Ernestoflores27/Garden_Defender/Mechanical Design/Renders/V2/1.JPG

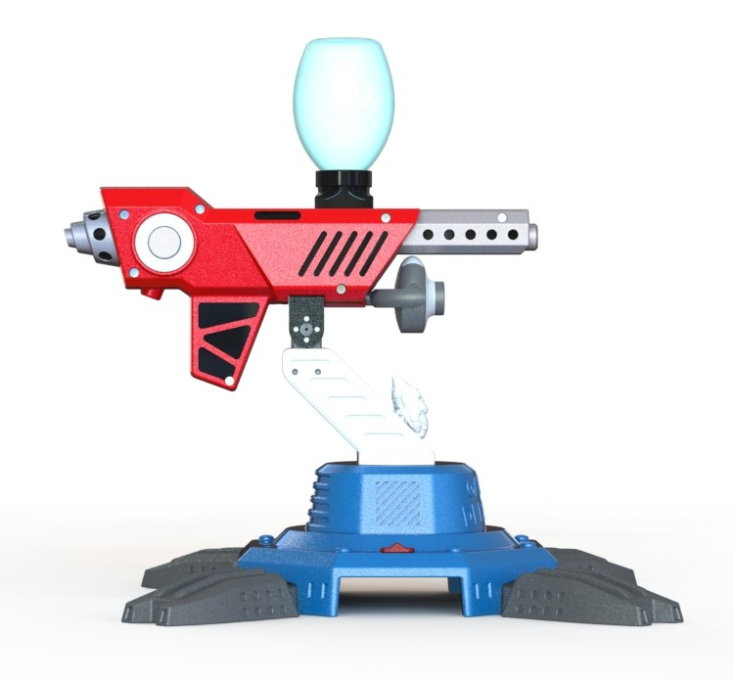
Mechanical Design/Renders/V2/1.JPG
