Ernestoflores27/Garden_Defender/Mechanical Design/Renders/V2/3.JPG

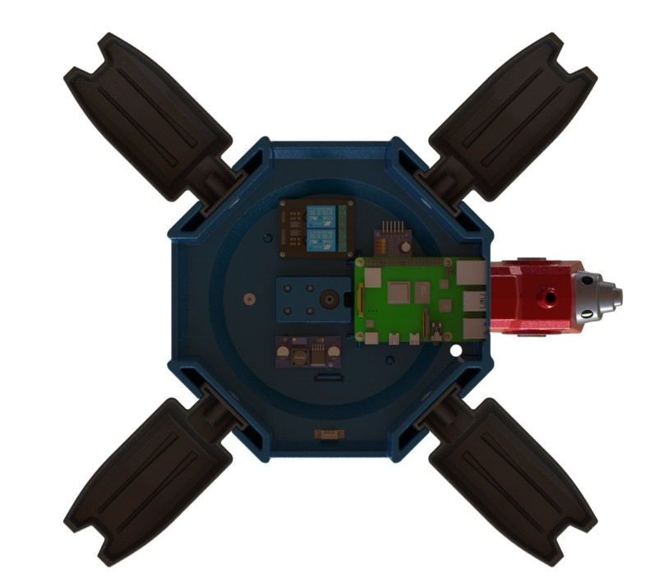
Mechanical Design/Renders/V2/3.JPG
