Ernestoflores27/Garden_Defender/Mechanical Design/STL Files/Foot_x4.STL

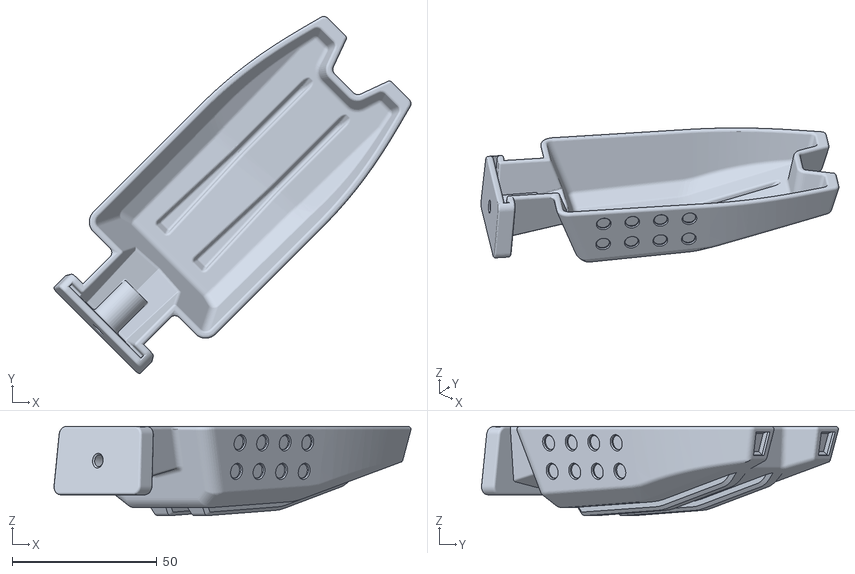
[picture p21: CAD file, 2023-04-01]
Mechanical Design/STL Files/Foot_x4.STL
123.1 x 123.1 x 30.8
