Ernestoflores27/Garden_Defender/Mechanical Design/SOLIDWORKS/Relay Module/Clamp Body.SLDPRT

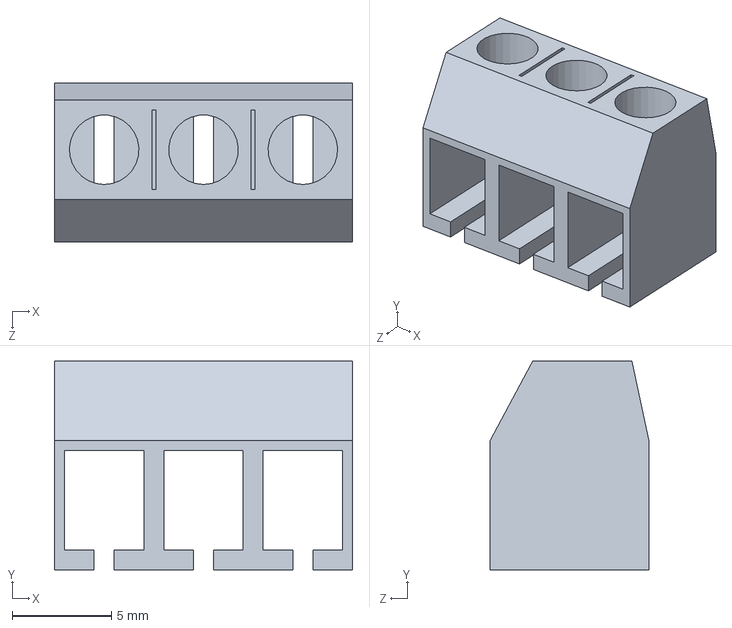
[picture p22: CAD file, 2023-02-25]
Mechanical Design/SOLIDWORKS/Relay Module/Clamp Body.SLDPRT
15.0 x 10.5 x 8.00 mm
