Ernestoflores27/Garden_Defender/Mechanical Design/STEP Files/Button_Predeterminado.STEP

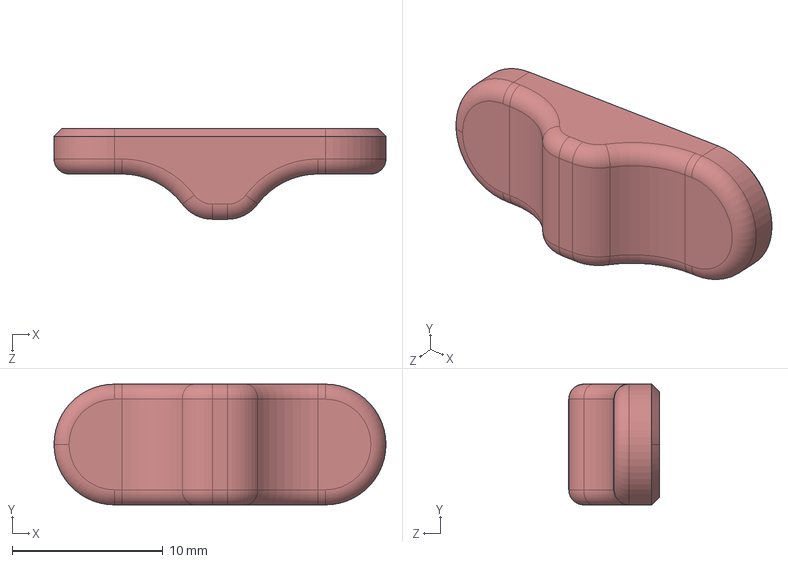
[picture p23: CAD file, 2023-02-25]
Mechanical Design/STEP Files/Button_Predeterminado.STEP
22.0 x 8.00 x 6.00 mm
