Ernestoflores27/Garden_Defender/Mechanical Design/STL Files/Blaster_Case_Barrel_Left.STL

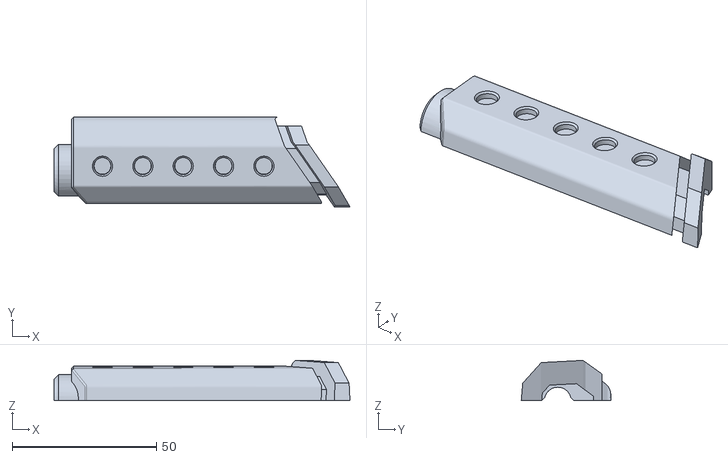
[picture p24: CAD file, 2023-02-25]
Mechanical Design/STL Files/Blaster_Case_Barrel_Left.STL
102.7 x 31.1 x 14.0
