Ernestoflores27/Garden_Defender/Mechanical Design/SOLIDWORKS/Heat Insert for Plastic_M4_94459A150.SLDPRT

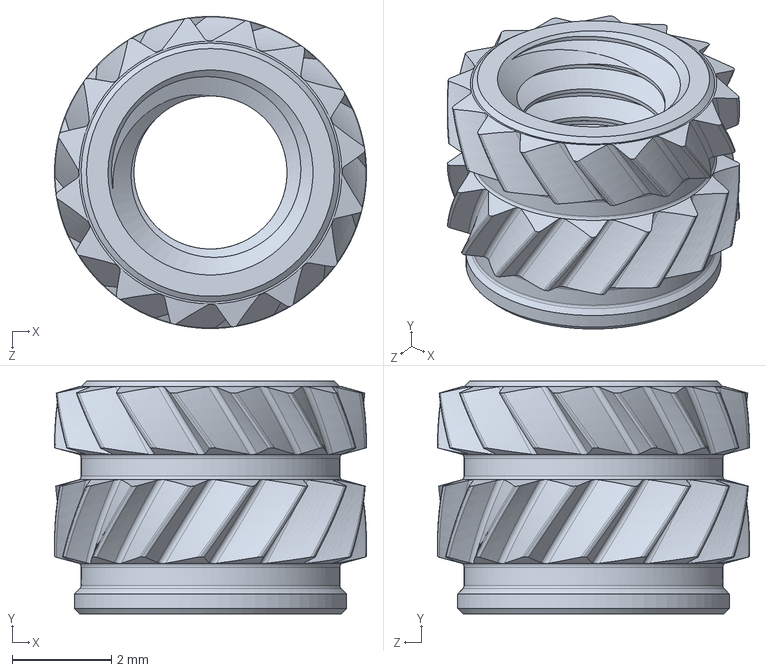
[picture p25: CAD file, 2023-02-25]
Mechanical Design/SOLIDWORKS/Heat Insert for Plastic_M4_94459A150.SLDPRT
6.30 x 4.70 x 6.30 mm
