Ernestoflores27/Garden_Defender/Mechanical Design/SOLIDWORKS/Relay Module/Relay Body.SLDPRT

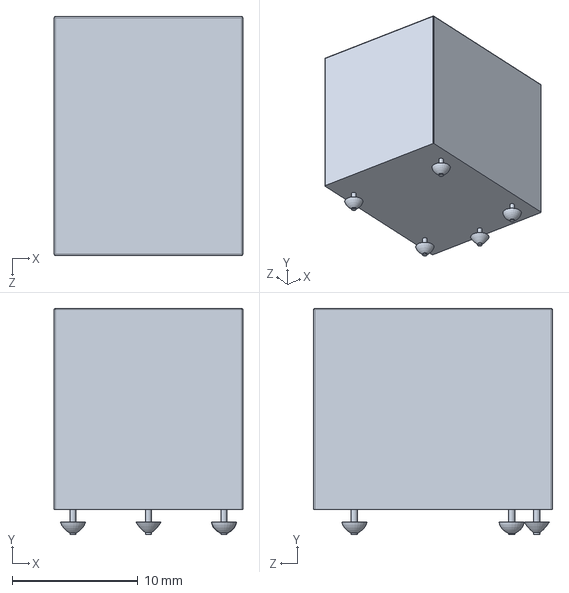
[picture p26: CAD file, 2023-02-25]
Mechanical Design/SOLIDWORKS/Relay Module/Relay Body.SLDPRT
15.0 x 18.0 x 19.0 mm
