Ernestoflores27/Garden_Defender/Mechanical Design/STEP Files/2PH63091A Board_Varsayılan.STEP

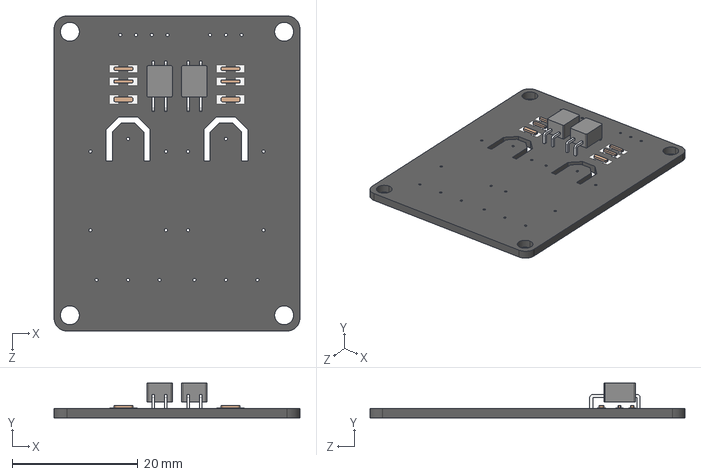
[picture p27: CAD file, 2023-02-25]
Mechanical Design/STEP Files/2PH63091A Board_Varsayılan.STEP
39.0 x 5.50 x 50.0 mm
