Ernestoflores27/Garden_Defender/Mechanical Design/STEP Files/Heat Insert for Plastic_94180A331_94180A331.STEP

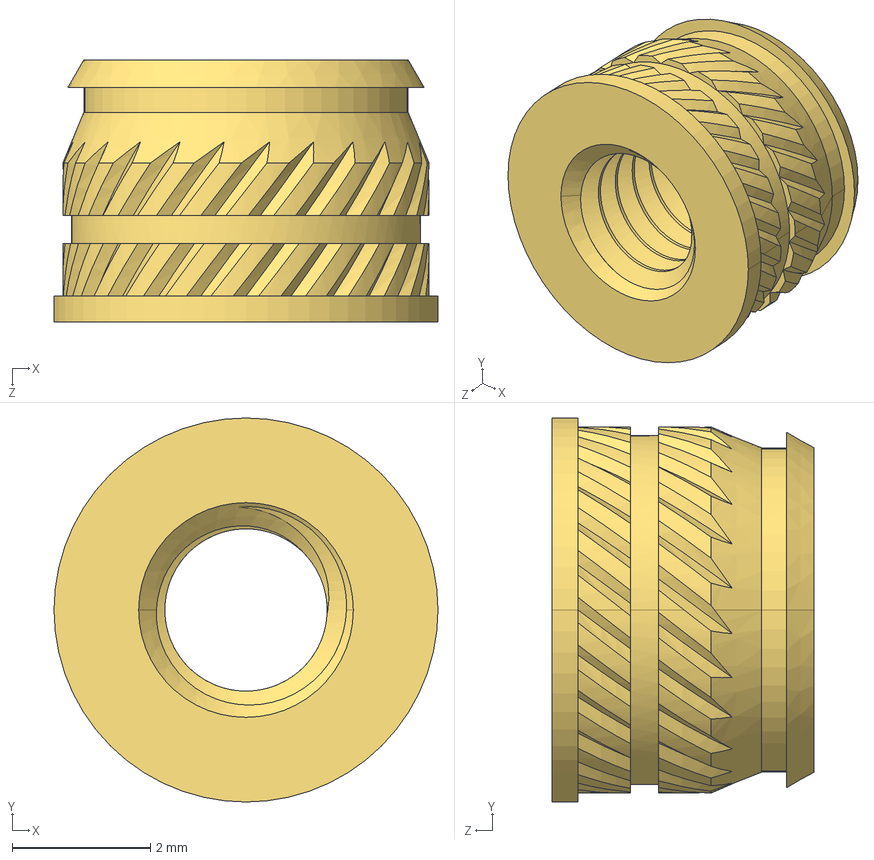
[picture p28: CAD file, 2023-02-25]
Mechanical Design/STEP Files/Heat Insert for Plastic_94180A331_94180A331.STEP
5.56 x 5.56 x 3.80 mm
