Ernestoflores27/Garden_Defender/Mechanical Design/STL Files/Blaster_Case_Ring_x2.STL

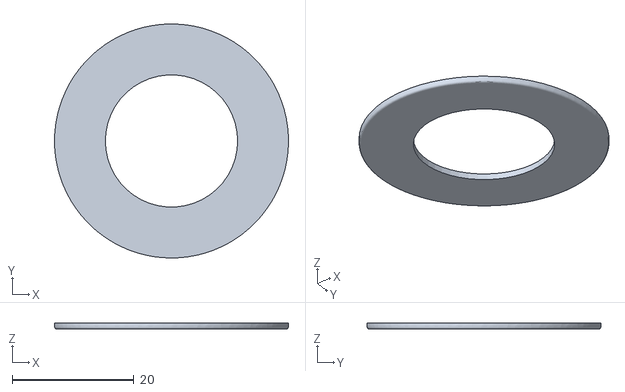
[picture p29: CAD file, 2023-02-25]
Mechanical Design/STL Files/Blaster_Case_Ring_x2.STL
38.4 x 38.4 x 1.00
