Ernestoflores27/Garden_Defender/Mechanical Design/STEP Files/Kern_ (1)^Copy of STEP-WE-PD-1280-rev1 v2_DC-DC XL6009_Predeterminado.STEP

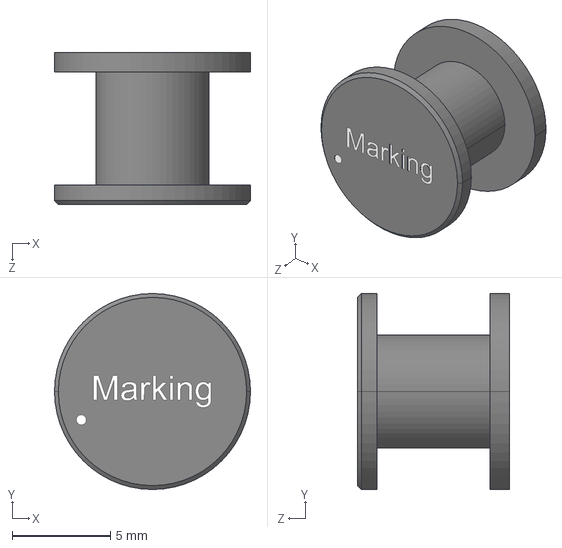
[picture p30: CAD file, 2023-02-25]
Mechanical Design/STEP Files/Kern_ (1)^Copy of STEP-WE-PD-1280-rev1 v2_DC-DC XL6009_Predeterminado.STEP
10.0 x 10.0 x 7.75 mm
