Ernestoflores27/Garden_Defender/Mechanical Design/STL Files/Blaster_Case_Right.STL

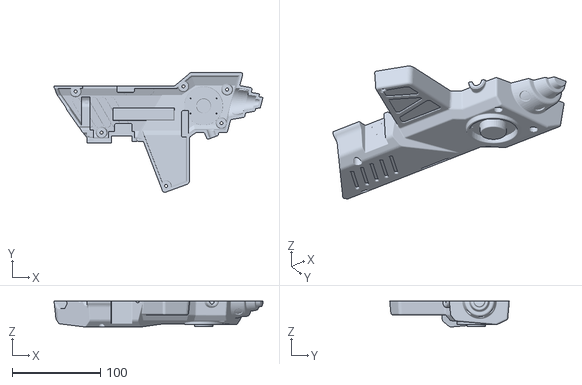
[picture p31: CAD file, 2023-02-25]
Mechanical Design/STL Files/Blaster_Case_Right.STL
237.1 x 135.7 x 29.4
