Ernestoflores27/Garden_Defender/Mechanical Design/STEP Files/Camera_Predeterminado.STEP

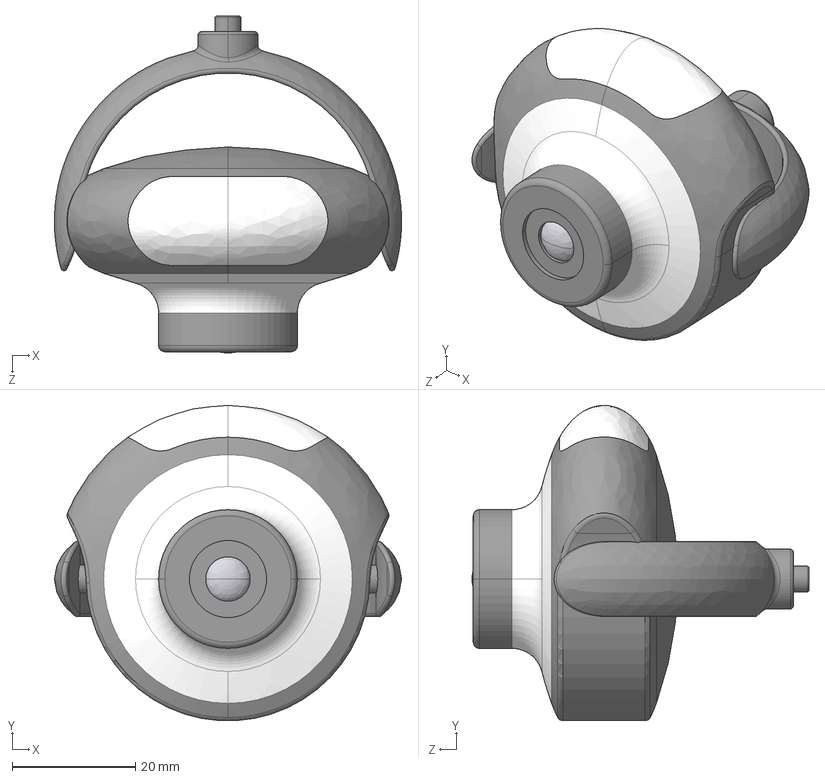
[picture p32: CAD file, 2023-02-25]
Mechanical Design/STEP Files/Camera_Predeterminado.STEP
56.3 x 51.1 x 54.6 mm
