Ernestoflores27/Garden_Defender/Mechanical Design/STL Files/Blaster_Case_Left.STL

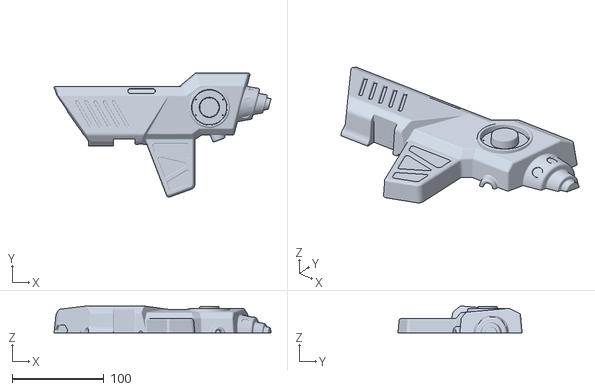
[picture p33: CAD file, 2023-02-25]
Mechanical Design/STL Files/Blaster_Case_Left.STL
237.1 x 135.7 x 29.4
