Ernestoflores27/Garden_Defender/Mechanical Design/STEP Files/Pin_ (1)^Copy of STEP-WE-PD-1280-rev1 v2_DC-DC XL6009_Predeterminado.STEP

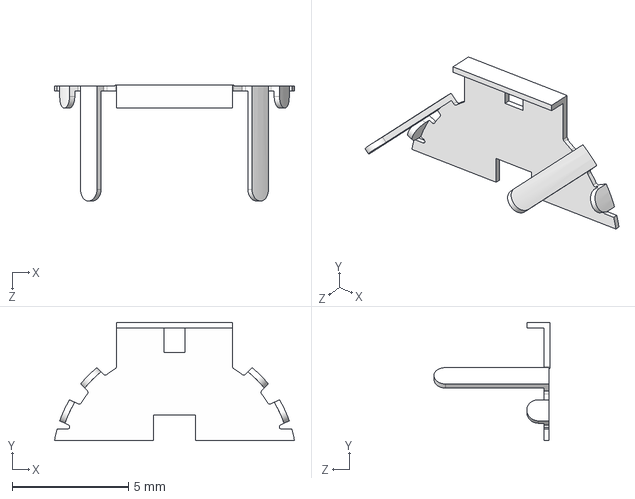
[picture p34: CAD file, 2023-02-25]
Mechanical Design/STEP Files/Pin_ (1)^Copy of STEP-WE-PD-1280-rev1 v2_DC-DC XL6009_Predeterminado.STEP
10.3 x 5.10 x 5.00 mm
