Ernestoflores27/Garden_Defender/Mechanical Design/SOLIDWORKS/Ball Bearing 5972K246.SLDPRT

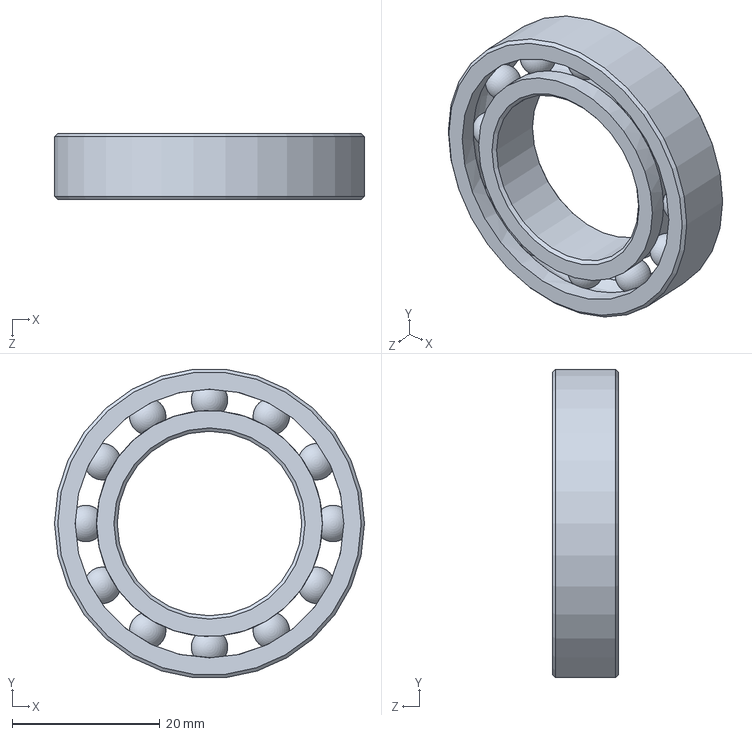
[picture p35: CAD file, 2023-02-16]
Mechanical Design/SOLIDWORKS/Ball Bearing 5972K246.SLDPRT
42.0 x 41.8 x 9.00 mm
