Ernestoflores27/Garden_Defender/Mechanical Design/SOLIDWORKS/Blaster.SLDPRT

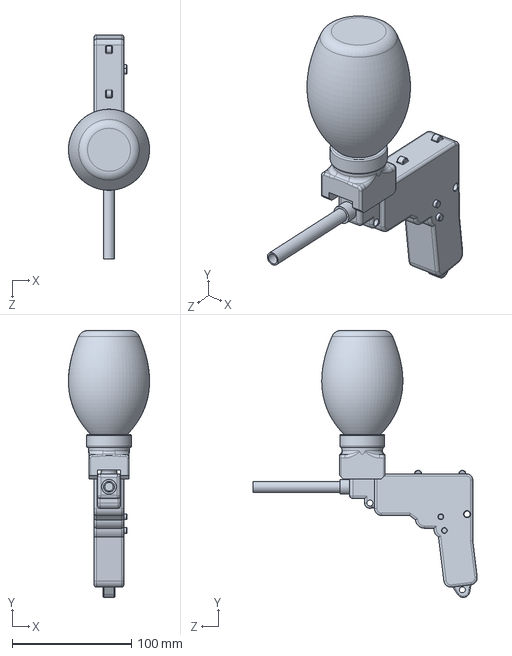
[picture p36: CAD file, 2023-02-15]
Mechanical Design/SOLIDWORKS/Blaster.SLDPRT
68.0 x 223.6 x 188.0 mm
