Ernestoflores27/Garden_Defender/Mechanical Design/STEP Files/Copy of Diode SMA v1^DC-DC XL6009_Predeterminado.STEP

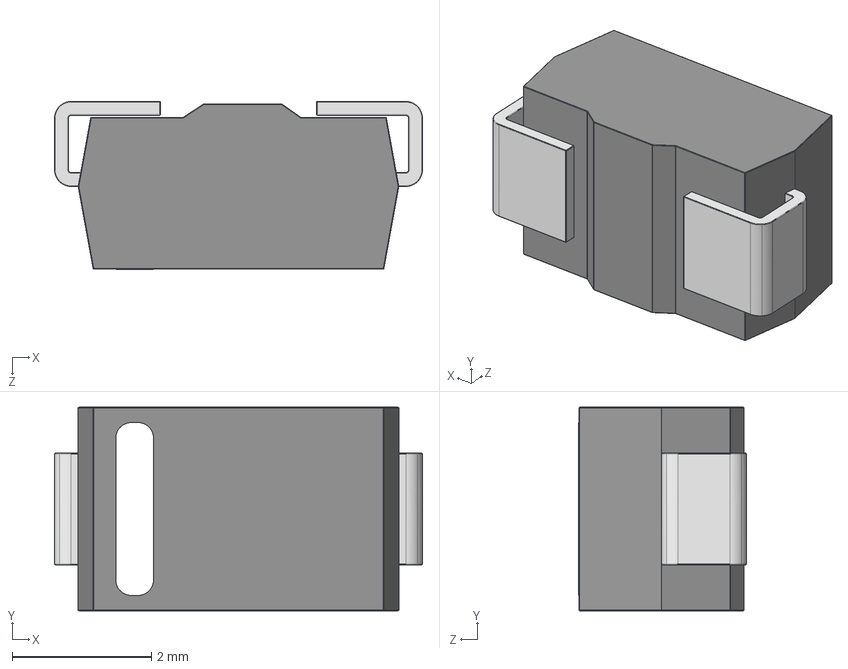
[picture p37: CAD file, 2023-02-25]
Mechanical Design/STEP Files/Copy of Diode SMA v1^DC-DC XL6009_Predeterminado.STEP
5.28 x 2.92 x 2.41 mm
