Ernestoflores27/Garden_Defender/Mechanical Design/STEP Files/Kern_^Copy of STEP-WE-PD-1280-rev1 v2_DC-DC XL6009_Predeterminado.STEP

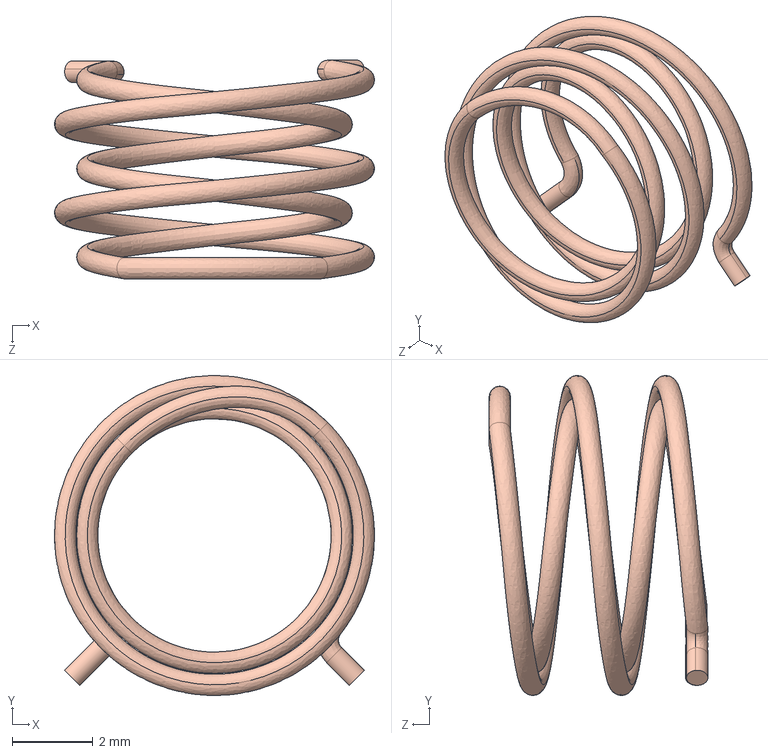
[picture p38: CAD file, 2023-02-25]
Mechanical Design/STEP Files/Kern_^Copy of STEP-WE-PD-1280-rev1 v2_DC-DC XL6009_Predeterminado.STEP
7.95 x 7.95 x 5.43 mm
