Ernestoflores27/Garden_Defender/Mechanical Design/STEP Files/Copy of TO263-5-1 v1^DC-DC XL6009_Predeterminado.STEP

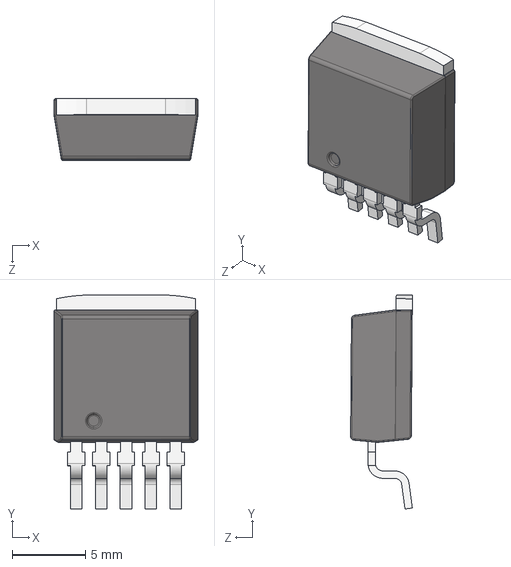
[picture p39: CAD file, 2023-02-25]
Mechanical Design/STEP Files/Copy of TO263-5-1 v1^DC-DC XL6009_Predeterminado.STEP
9.82 x 14.6 x 4.22 mm
