Ernestoflores27/Garden_Defender/Mechanical Design/STEP Files/Copy of Board_XL6009 v1^DC-DC XL6009_Predeterminado.STEP

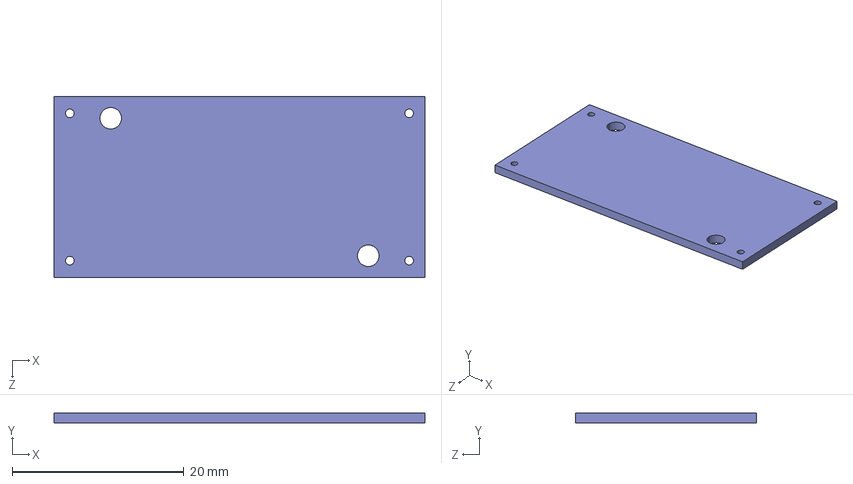
[picture p40: CAD file, 2023-02-25]
Mechanical Design/STEP Files/Copy of Board_XL6009 v1^DC-DC XL6009_Predeterminado.STEP
43.2 x 1.20 x 21.1 mm
