Ernestoflores27/Garden_Defender/Mechanical Design/STEP Files/LDX-218_Mounting_Disk_Predeterminado.STEP

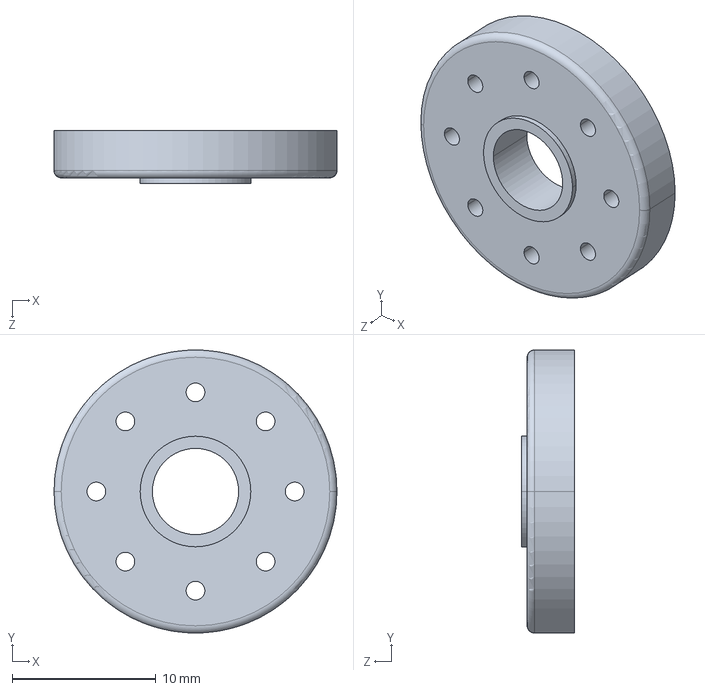
[picture p41: CAD file, 2023-02-25]
Mechanical Design/STEP Files/LDX-218_Mounting_Disk_Predeterminado.STEP
19.7 x 19.7 x 3.70 mm
