Ernestoflores27/Garden_Defender/Mechanical Design/STEP Files/Clamp Body_Varsayılan.STEP

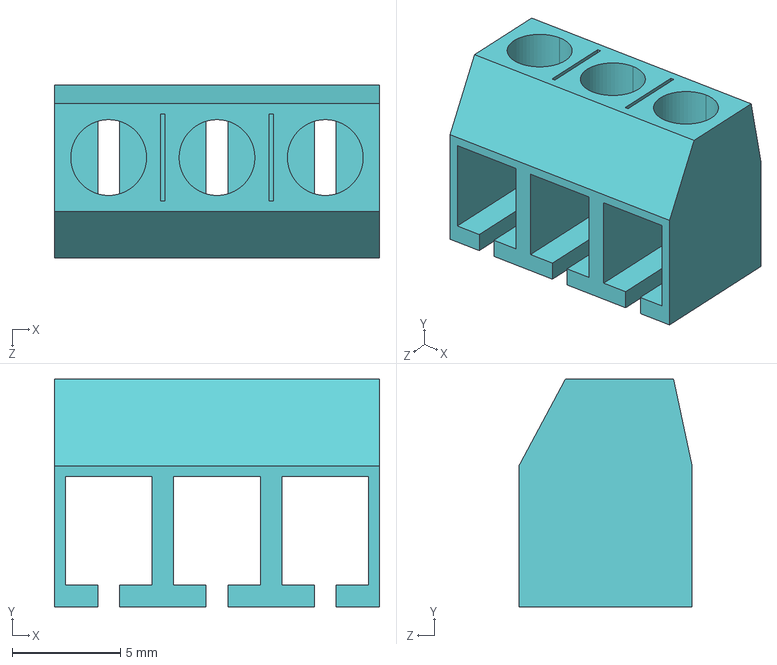
[picture p42: CAD file, 2023-02-25]
Mechanical Design/STEP Files/Clamp Body_Varsayılan.STEP
15.0 x 10.5 x 8.00 mm
