Ernestoflores27/Garden_Defender/Mechanical Design/STEP Files/Copy of 3296W v3^DC-DC XL6009_Predeterminado.STEP

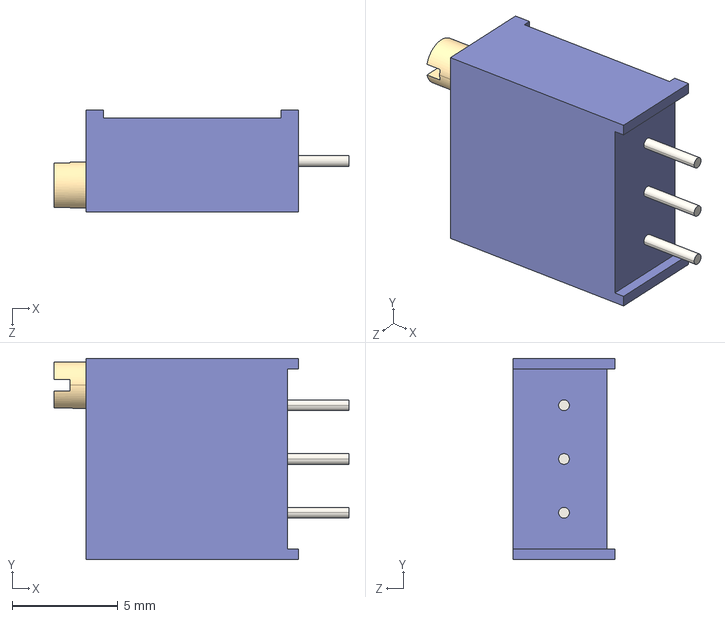
[picture p43: CAD file, 2023-02-25]
Mechanical Design/STEP Files/Copy of 3296W v3^DC-DC XL6009_Predeterminado.STEP
14.0 x 9.53 x 4.83 mm
