Ernestoflores27/Garden_Defender/Mechanical Design/STEP Files/Copy of CAPAE-D8.0x10.2 v1^DC-DC XL6009_Predeterminado.STEP

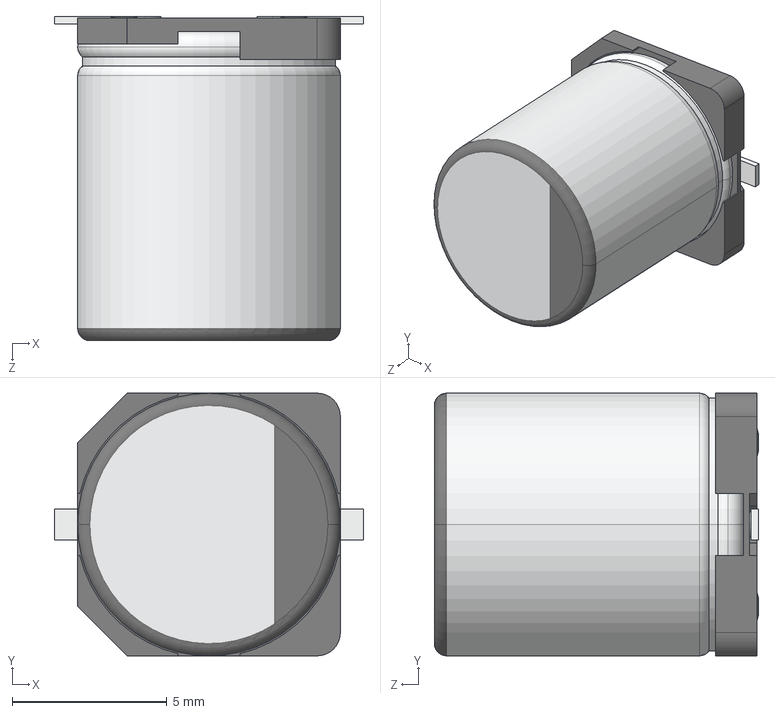
[picture p44: CAD file, 2023-02-25]
Mechanical Design/STEP Files/Copy of CAPAE-D8.0x10.2 v1^DC-DC XL6009_Predeterminado.STEP
10.0 x 8.50 x 10.5 mm
