Ernestoflores27/Garden_Defender/Mechanical Design/STEP Files/Kern_ (2)^Copy of STEP-WE-PD-1280-rev1 v2_DC-DC XL6009_Predeterminado.STEP

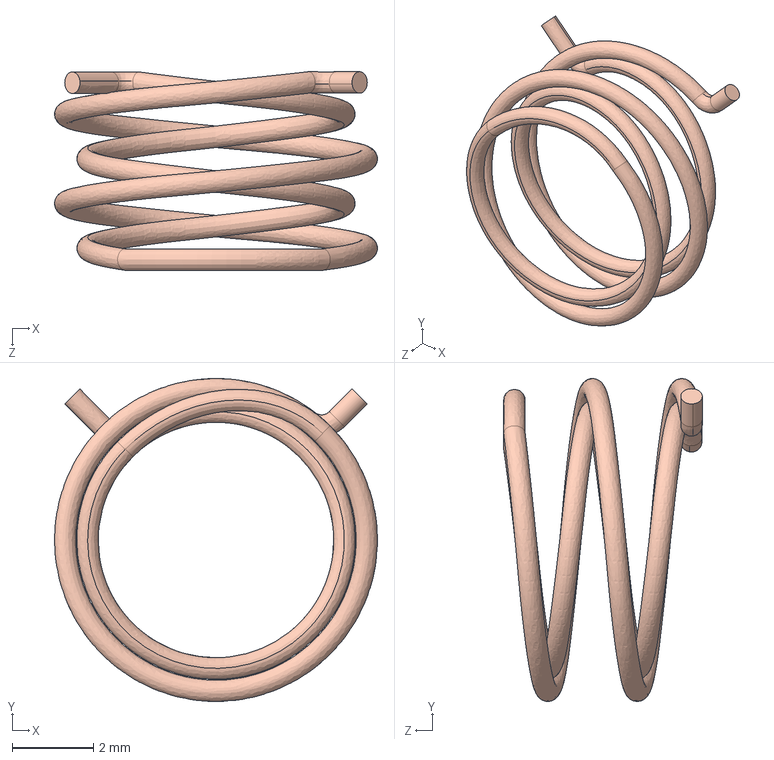
[picture p45: CAD file, 2023-02-25]
Mechanical Design/STEP Files/Kern_ (2)^Copy of STEP-WE-PD-1280-rev1 v2_DC-DC XL6009_Predeterminado.STEP
7.95 x 7.95 x 4.89 mm
