Ernestoflores27/Garden_Defender/assets/TestServos.png

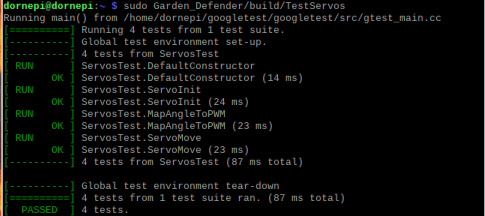
assets/TestServos.png
