Ernestoflores27/Garden_Defender/assets/TestTurret.png

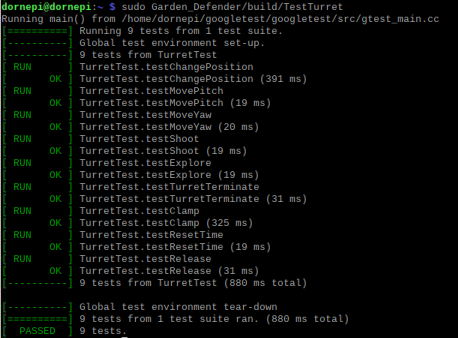
assets/TestTurret.png
