Ernestoflores27/Garden_Defender/Objects/Object.cpp

#include "Object.h"
/**
 * @brief Construct a new Object:: Object object()
 * 
 * @param object 
 * @param camera_width 
 * @param camera_height 
 */
Object::Object(cv::Rect object, int camera_width, int camera_height)
{
    x = object.x;
    y = object.y;
    h = object.height;
    w = object.width;

    center_x = x + (w / 2);
    center_y = y + (h / 2);

    offset_x = (camera_width / 2) - center_x;
    offset_y = (camera_height / 2) - center_y;

    distance = (offset_x * offset_x) + (offset_y * offset_y);
}
/**
 * @brief Compare distance of multiple detections
 * 
 * @param s1 
 * @param s2 
 * @return true 
 * @return false 
 */
bool operator<(const Object &s1, const Object &s2)
{
    return s1.distance < s2.distance;
}
